jalmx/base_esp32/docs/proyecto/licencia.md

# Licencia

## MIT License

```
The MIT License (MIT)

Copyright (c) 2024 Xizuth

Permission is hereby granted, free of charge, to any person obtaining a copy
of this software and associated documentation files (the "Software"), to deal
in the Software without restriction, including without limitation the rights
to use, copy, modify, merge, publish, distribute, sublicense, and/or sell
copies of the Software, and to permit persons to whom the Software is
furnished to do so, subject to the following conditions:

The above copyright notice and this permission notice shall be included in all
copies or substantial portions of the Software.

THE SOFTWARE IS PROVIDED "AS IS", WITHOUT WARRANTY OF ANY KIND, EXPRESS OR
IMPLIED, INCLUDING BUT NOT LIMITED TO THE WARRANTIES OF MERCHANTABILITY,
FITNESS FOR A PARTICULAR PURPOSE AND NONINFRINGEMENT. IN NO EVENT SHALL THE
AUTHORS OR COPYRIGHT HOLDERS BE LIABLE FOR ANY CLAIM, DAMAGES OR OTHER
LIABILITY, WHETHER IN AN ACTION OF CONTRACT, TORT OR OTHERWISE, ARISING FROM,
OUT OF OR IN CONNECTION WITH THE SOFTWARE OR THE USE OR OTHER DEALINGS IN THE
SOFTWARE.
```

## Aplicabilidad

Esta licencia cubre:

- ✅ **Código fuente** (firmware de ejemplo, scripts)
- ✅ **Documentación** (archivos .md, imágenes generadas)
- ✅ **Diseño hardware** (esquemáticos KiCad, PCB layout, librerías)
- ✅ **Archivos de fabricación** (Gerber, BOM, Pick&Place)

## Exclusiones

- ❌ **Datasheets** de componentes (propiedad de fabricantes)
- ❌ **Modelos 3D** de terceros (ver créditos en [about/creditos.md](../about/creditos.md))
- ❌ **Logos de marcas** (Espressif, KiCad, etc.)

## Uso comercial

La licencia MIT **permite uso comercial** sin restricciones. Puedes:

- Fabricar y vender la PCB
- Incluirla en productos comerciales
- Modificar el diseño para tus necesidades
- Distribuir versiones modificadas

Solo se requiere **mantener el aviso de copyright** y la licencia en copias sustanciales.

## Archivo original

Ver [LICENSE.md](../../LICENSE.md) en la raíz del repositorio.
