jalmx/base_esp32/assets/raw.pdf

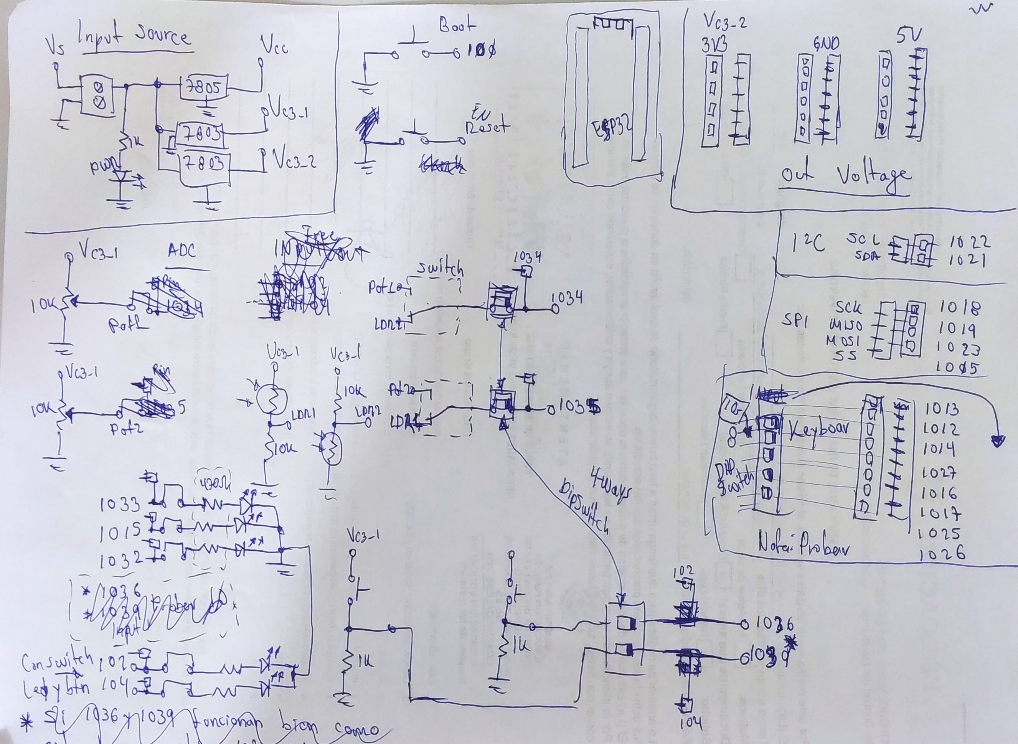
[picture p10: page 1]
