jalmx/base_esp32/fritzing/base_esp32_w.png

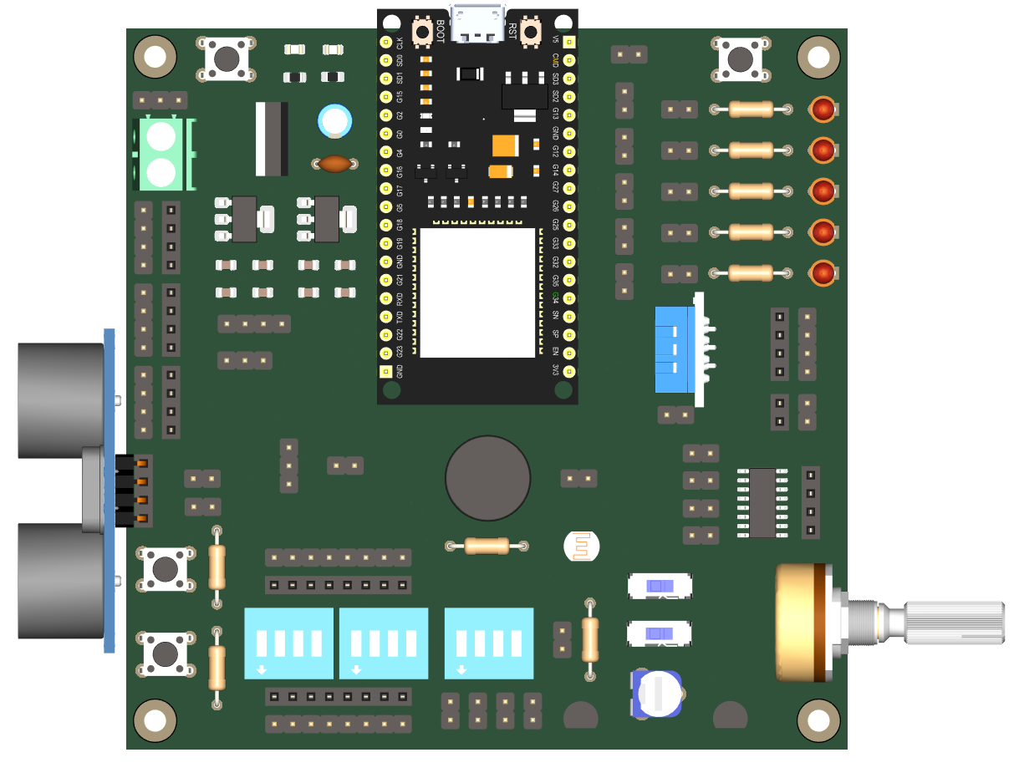
fritzing/base_esp32_w.png
