jalmx/base_esp32/fritzing/board_render_blue.png

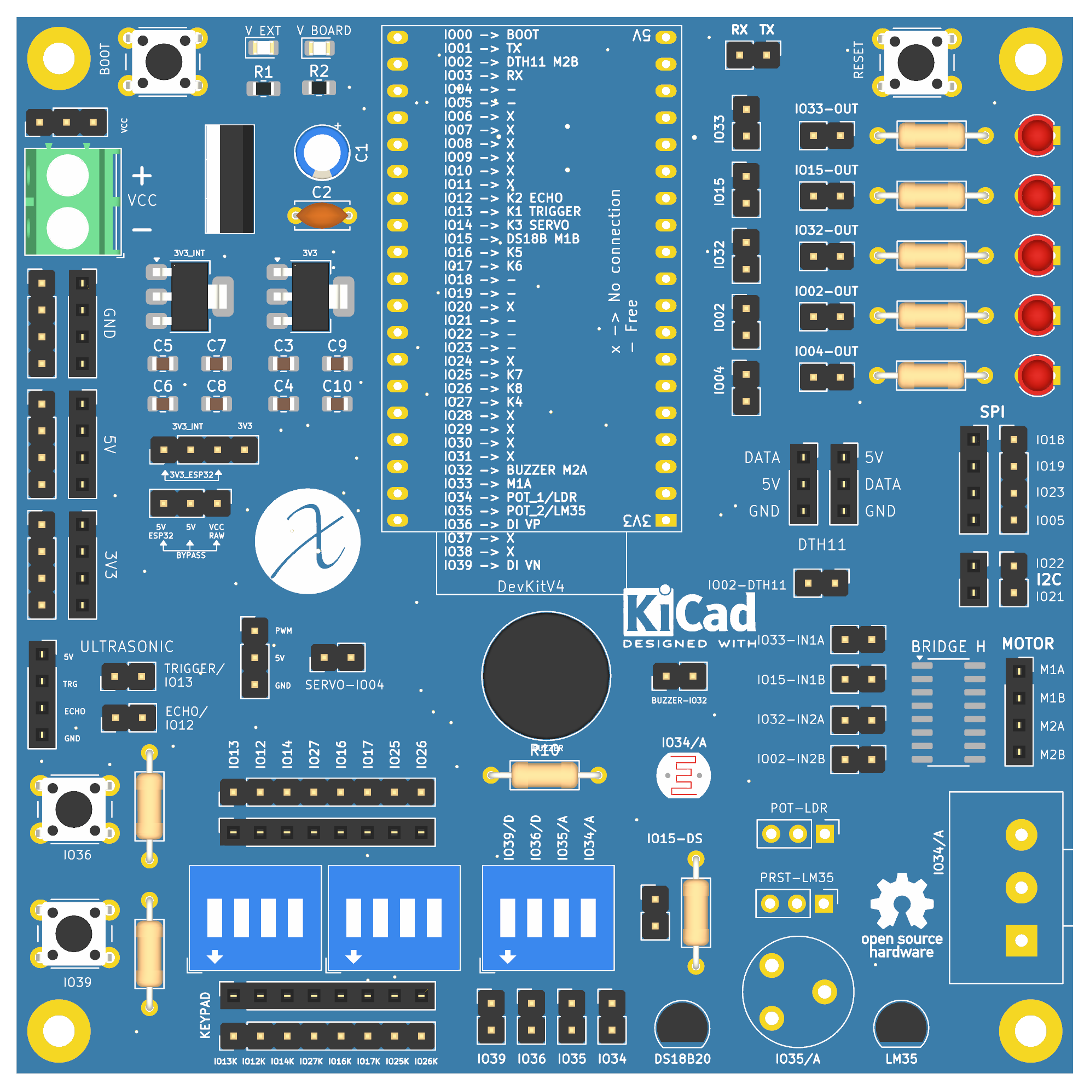
fritzing/board_render_blue.png
