jalmx/base_esp32/pcb/base_esp32-B_Cu.png

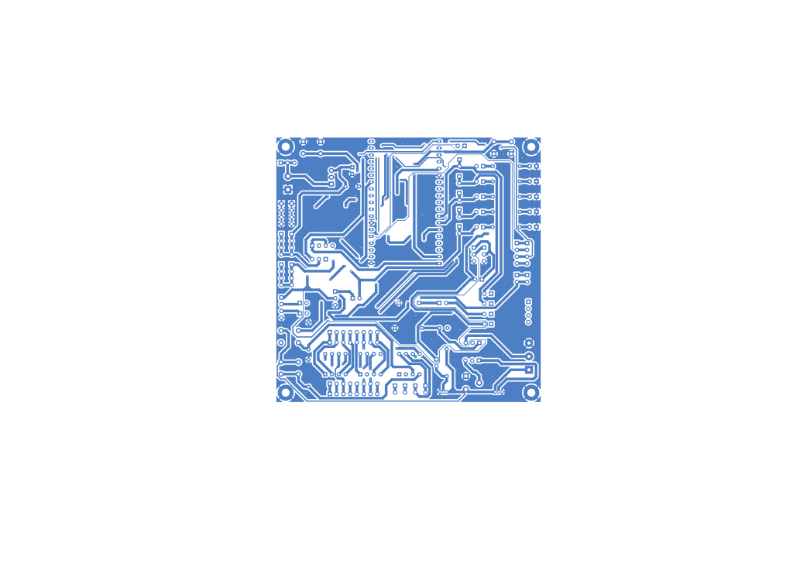
pcb/base_esp32-B_Cu.png
