jalmx/base_esp32/pcb/base_esp32-B_Mask.png

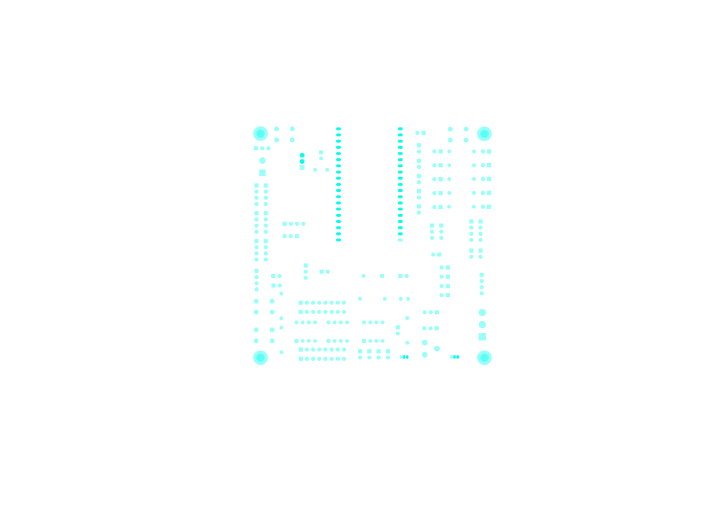
pcb/base_esp32-B_Mask.png
