jalmx/base_esp32/pcb/base_esp32-Edge_Cuts.png

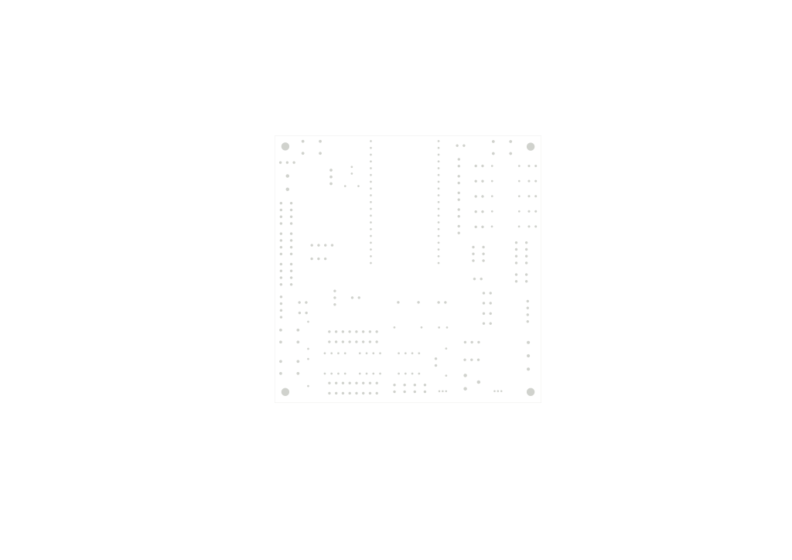
pcb/base_esp32-Edge_Cuts.png
