jalmx/base_esp32/pcb/base_esp32-F_Cu.png

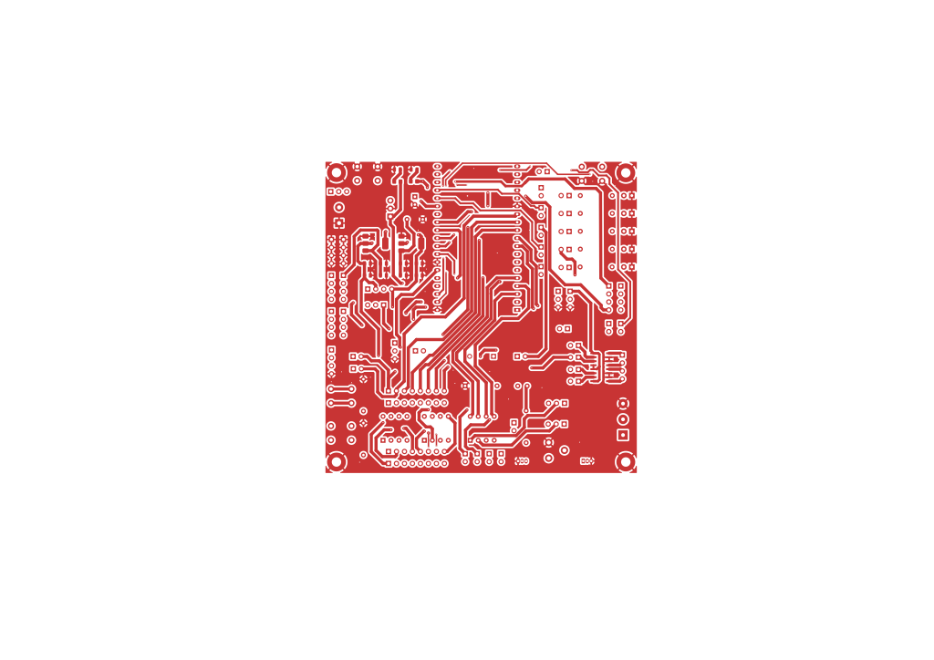
pcb/base_esp32-F_Cu.png
